gotree94/AR_Glass_Robot_Control/AprilTag_6개_20_0mm/AprilTag_6개_전체.png

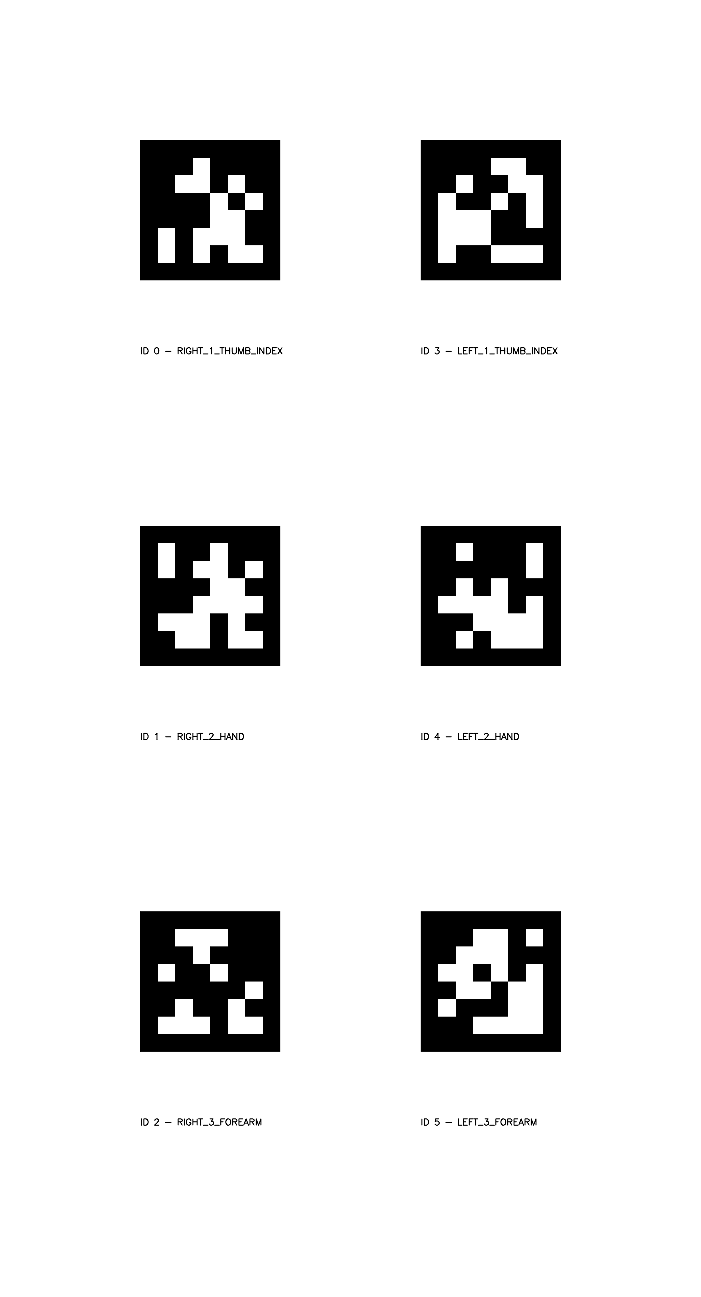
AprilTag_6개_20_0mm/AprilTag_6개_전체.png
