gotree94/AR_Glass_Robot_Control/AprilTag_6개_20_0mm/ID_0_RIGHT_1_THUMB_INDEX.png

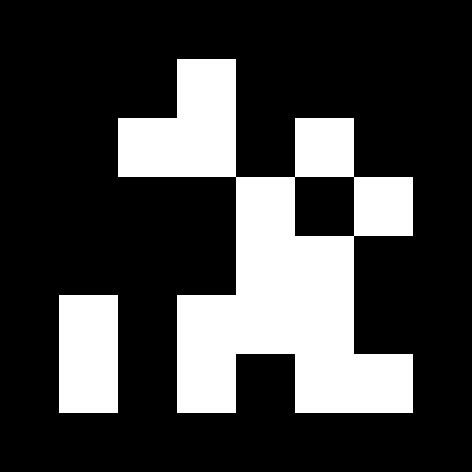
AprilTag_6개_20_0mm/ID_0_RIGHT_1_THUMB_INDEX.png
