gotree94/AR_Glass_Robot_Control/AprilTag_6개_20_0mm/ID_3_LEFT_1_THUMB_INDEX.png

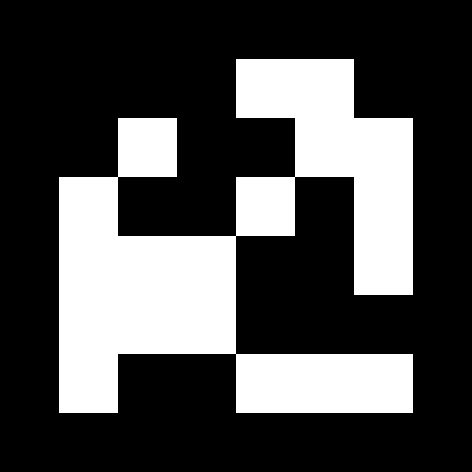
AprilTag_6개_20_0mm/ID_3_LEFT_1_THUMB_INDEX.png
