gotree94/AR_Glass_Robot_Control/AprilTag_6개_20_0mm/ID_4_LEFT_2_HAND.png

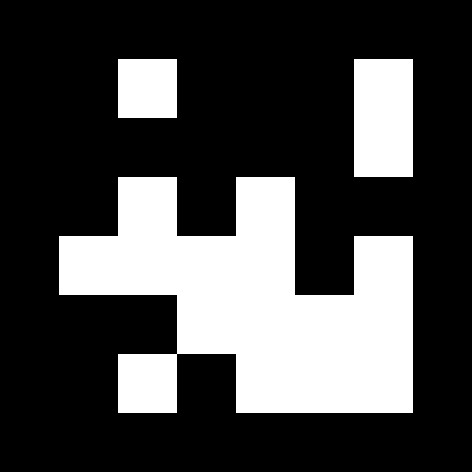
AprilTag_6개_20_0mm/ID_4_LEFT_2_HAND.png
