gotree94/AR_Glass_Robot_Control/AprilTag_6개_20_0mm/ID_5_LEFT_3_FOREARM.png

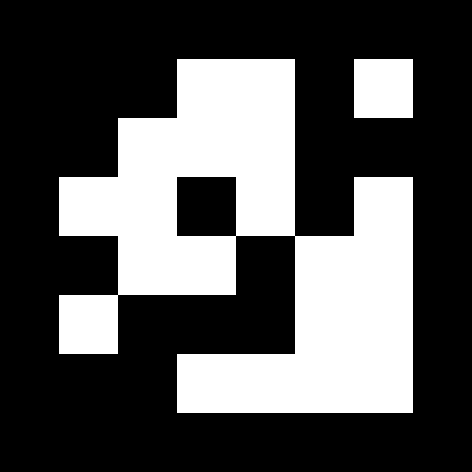
AprilTag_6개_20_0mm/ID_5_LEFT_3_FOREARM.png
