gotree94/AR_Glass_Robot_Control/AR-Glass/esp32-cam-mb/ESP32-CAM-MB v1.jpg

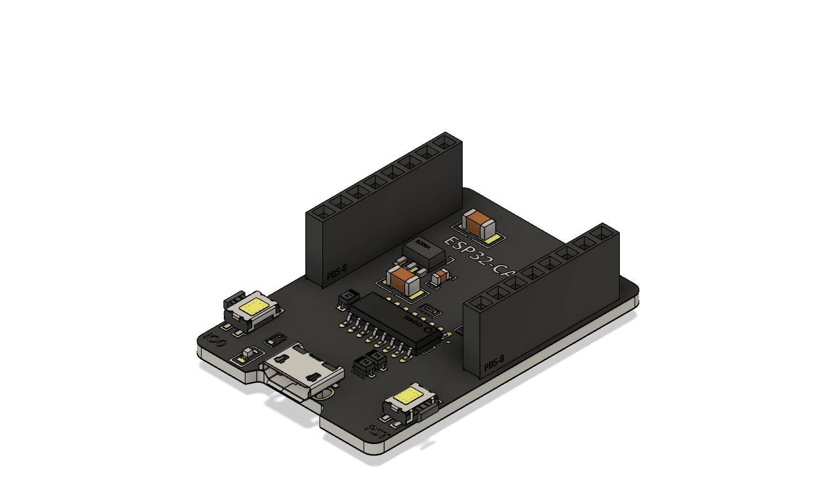
AR-Glass/esp32-cam-mb/ESP32-CAM-MB v1.jpg
