gotree94/AR_Glass_Robot_Control/AR-Glass/esp32-cam-mb/ESP32-CAM-MB_view.jpg

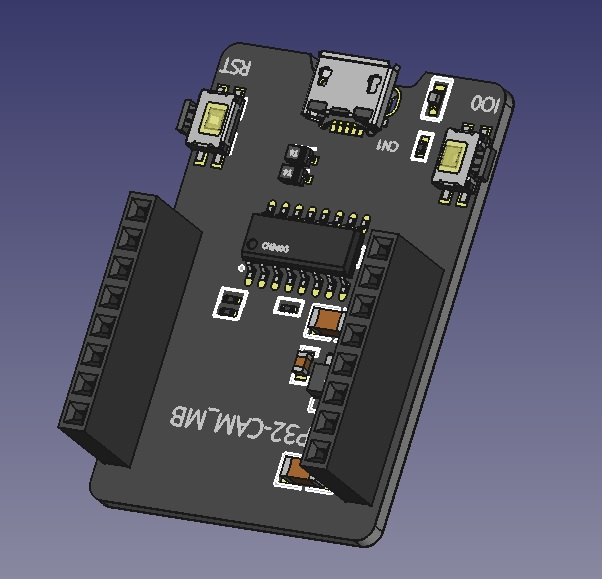
AR-Glass/esp32-cam-mb/ESP32-CAM-MB_view.jpg
